Fliperdo/CS-4911-PipBoy-Project/Production_Menu_System/Pip-Boy_4000/Driver/data/Snowy.jpg

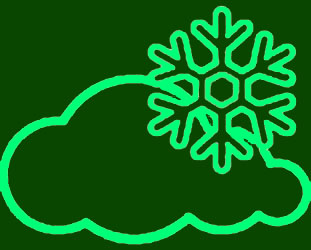
Production_Menu_System/Pip-Boy_4000/Driver/data/Snowy.jpg
