Fliperdo/CS-4911-PipBoy-Project/Production_Menu_System/Pip-Boy_4000/Driver/Calendar_Class.pde

class Calendar implements MenuItem {
  String hello;
  
  Calendar(State mainState) {
    hello = "hello from calendar.display();";
  }
  
  void display(){
//    println(hello);
  }
  
  void touched(int x,int y){
  }
  
  
}
