Fliperdo/CS-4911-PipBoy-Project/Production_Menu_System/Pip-Boy_4000/Driver/Camera_Class.pde

class Camera implements MenuItem {
  String hello;
  State mainState;
  PImage pic;
  
  Camera(State mainState) {
    hello = "hello from camera.display();";
    this.mainState = mainState;
  }
  
  void display(){
    mainState.updateCameraImage();
    pic = mainState.getCameraImage();
    if(pic != null) {
      image(pic, 0 , 0);
    }    
  }
  
  void touched(int x,int y){
  }
  
  
}

//CAPTURE CLASS
