Fliperdo/CS-4911-PipBoy-Project/Production_Menu_System/Pip-Boy_4000/Driver/Map_Class.pde

class Map implements MenuItem {
  String hello;
  
  Map(State mainState) {
    hello = "hello from map.display();";
  }
  
  void display(){
    println(hello);
  }
  
  void touched(int x,int y){
  }
  
  
}
